kasedy/esp8266-wifi-led-dimmer/src/MqttProcessor.cpp

#include "MqttProcessor.h"
#include "config.h"
#include "dbg.h"
#include "LightController.h"

#include <ESP8266WiFi.h>
#include <Ticker.h>
#include <AsyncMqttClient.h>
#include <ArduinoJson.h>

extern LightController *lightController;

namespace MqttProcessor {
  AsyncMqttClient mqttClient;
  Ticker mqttReconnectTimer;

  void connectToMqtt() {
    if (!WiFi.isConnected()) {
      DBG("Trying to connect MQTT but WiFi is not connected!\n");
      mqttReconnectTimer.once(10, connectToMqtt);
    } else if (!mqttClient.connected()) {
      DBG("Connecting to MQTT...\n");
      mqttClient.connect();
    }
  }

  void onMqttConnect(bool sessionPresent) {
    DBG("Connected to MQTT. Session present: %d\n", sessionPresent);
    mqttClient.subscribe(LED_CONFIG_MQTT_TOPIC_COMMAND, 1);

    DynamicJsonDocument doc(1024);
    doc[F("schema")] = F("json");
    doc[F("unique_id")] = HOSTNAME;
    doc[F("name")] = DEVICE_FULL_NAME;
    doc[F("state_topic")] = LED_CONFIG_MQTT_TOPIC_STATE;
    doc[F("command_topic")] = LED_CONFIG_MQTT_TOPIC_COMMAND;
    doc[F("brightness")] = true;
    doc[F("optimistic")] = false;
    doc[F("qos")] = 2;
    doc[F("retain")] = true;
    doc[F("effect")] = lightController->getAnimationCount() > 0;
    doc[F("white_value")] = true;

    if (lightController->getAnimationCount() > 0) {
      JsonArray effectList = doc.createNestedArray(F("effect_list"));
      for (size_t i = 0; i < lightController->getAnimationCount(); ++i) {
        effectList.add(lightController->getAnimationName(i));
      }
    }
    
    String output;
    serializeJson(doc, output);
    doc.clear();

    DBG("Sending discovery config: %s\n", output.c_str());
    mqttClient.publish(LED_CONFIG_MQTT_TOPIC_CONFIG, 2, true, output.c_str(), output.length());
  }

  void onMqttDisconnect(AsyncMqttClientDisconnectReason reason) {
    DBG("Disconnected from MQTT. Rery in 10 sec. Error code %d\n", reason);
    mqttReconnectTimer.once(10, connectToMqtt);
  }

  void broadcastStateViaMqtt() {
    if (!mqttClient.connected()) {
      DBG("Unable to publish the state to MQTT. Client is not connected.\n");
      return;
    }

    StaticJsonDocument<JSON_OBJECT_SIZE(20)> doc;

    doc[F("state")] = lightController->isOn() ? CONFIG_MQTT_PAYLOAD_ON : CONFIG_MQTT_PAYLOAD_OFF;
    doc[F("brightness")] = lightController->getLightBrightness();
    if (lightController->getCurrentAnimationIndex() != -1) {
      doc[F("effect")] = lightController->getCurrentAnimationName();
    }
    doc[F("white_value")] = lightController->getAnimationSpeed();

    size_t jsonSize = measureJson(doc);
    char buffer[jsonSize + 1];
    serializeJson(doc, buffer, sizeof(buffer));

    const char* topic = LED_CONFIG_MQTT_TOPIC_STATE;
    DBG("Publishing state to %s -> %s\n", topic, buffer);
    mqttClient.publish(topic, 2, false, buffer, jsonSize);
  }

  void onMqttMessage(char* topic, char* payload, AsyncMqttClientMessageProperties properties, size_t length, size_t index, size_t total) {
    DBG("Message arrived [%s]\n", topic);

    char message[length + 1];
    memcpy(message, payload, length);
    message[length] = '\0';
    DBG("%s\n", message);
    
    StaticJsonDocument<JSON_OBJECT_SIZE(20)> doc;
    DeserializationError error = deserializeJson(doc, message);

    if (error) {
      DBG("parseObject() failed\n");
      return;
    }

    if (doc.containsKey(F("state"))) {
      const char *state = doc[F("state")];
      DBG("State = %s\n", state);
      if (strcmp(state, CONFIG_MQTT_PAYLOAD_ON) == 0) {
        DBG("Switching ON\n");
        lightController->setStateOn(true);
      }
      else if (strcmp(state, CONFIG_MQTT_PAYLOAD_OFF) == 0) {
        DBG("Switching OFF\n");
        lightController->setStateOn(false);
      }
    }

    if (doc.containsKey(F("brightness"))) {
      lightController->setLightBrightness(doc[F("brightness")]);
    }

    if (doc.containsKey(F("effect"))) {
      lightController->setAnimationByName(doc[F("effect")]);
    }

    if (doc.containsKey(F("white_value"))) {
      lightController->setAnimationSpeed(doc[F("white_value")]);
    }
  }

  void setup() {
    mqttClient
      .onConnect(onMqttConnect)
      .onDisconnect(onMqttDisconnect)
      .onMessage(onMqttMessage)
      .setClientId(HOSTNAME)
      .setServer(MQTT_SERVER, MQTT_PORT);
    connectToMqtt();
  }
};
