kasedy/esp8266-wifi-led-dimmer/src/animations/FadeCycle.h

#pragma once

#include "animations/BaseAnimation.h"
#include <stdint.h>

/*
 * Fade evenly from max brigtness to 0 and back;
 */
class FadeCycle : public BaseAnimation {
  uint8_t actualBrightness;
  int8_t step = -1;
  unsigned long lastUpdateTime = 0;

  void changeBrightness(uint8_t newBrightness);
  unsigned long getUpdateInterval();

public:
  FadeCycle(LightController *lightController);
  virtual ~FadeCycle();
  virtual void handle() override;

  static Effect effect(const char* name);
};
