kasedy/esp8266-wifi-led-dimmer/src/animations/FadeSwitch.cpp

#include "animations/FadeSwitch.h"

#include "dbg.h"
#include "helpers.h"
#include "LightController.h"

FadeSwitch::FadeSwitch(LightController *lightController) : 
    BaseAnimation(lightController) {
  DBG("FadeSwitch constructed;\n");
}

FadeSwitch::~FadeSwitch() {
  DBG("FadeSwitch destroyed;\n");
}

void FadeSwitch::handle() {
  if (lightController->isMaxBrightensChanged() 
      || lightController->isEffectChanged()) {
    updateBrightness(getEndBrightness());
    return;
  }

  if (currentBrightness == getEndBrightness()
      || micros() - lastUpdateTime < getUpdateInterval()) {
    return;
  }
  updateBrightness(currentBrightness + sgn(getEndBrightness(), currentBrightness));
}

void FadeSwitch::updateBrightness(uint8_t newValue) {
    lastUpdateTime = micros();
    currentBrightness = newValue;
    lightController->setAllPinValue(currentBrightness);
}

uint8_t FadeSwitch::getEndBrightness() const {
  return lightController->isOn() ? lightController->getLightBrightness() : 0;
}

uint8_t FadeSwitch::getStartBrightness() const {
  return lightController->isOn() ? 0 : lightController->getLightBrightness();
}

unsigned long FadeSwitch::getUpdateInterval() {
  int32_t multiplier = map(lightController->getAnimationSpeed(), 0, 255, -50, 50);
  uint8_t brightnessDifference = difference(getEndBrightness(), getStartBrightness());
  if (brightnessDifference == 0) {
    return -1;
  }
  unsigned long refreshInterval = 1000000 / brightnessDifference; // microseconds
  if (multiplier < 0) {
    refreshInterval += refreshInterval * (-multiplier) / 10;
  } else if (multiplier > 0) {
    refreshInterval = refreshInterval * 10 / (multiplier + 10);
  } 
  return refreshInterval;
}

Effect FadeSwitch::effect(const char* name) {
  return {name, [] (LightController *lightController) -> BaseAnimation* { return new FadeSwitch(lightController); }, 1};
}
