kasedy/esp8266-wifi-led-dimmer/src/animations/all.h

#pragma once

#include "animations/NoAnimation.h"
#include "animations/FadeCycle.h"
#include "animations/FadeSwitch.h"
#include "animations/RandomSplashes.h"
#include "animations/RandomSplashesCompensated.h"
#include "animations/SingleLedFade.h"
